wodiesan/senior_design_spring/documentation/latex_calculations/main.tex

\documentclass[12pt]{article}
%\usepackage{fontspec}
%\usepackage[utf8]{inputenc}

\usepackage[margin=1in]{geometry}

\usepackage{graphicx}
\usepackage{amsmath}
\usepackage{float}
\usepackage{xfrac}
%\usepackage{subfig}
\usepackage{subcaption}
\captionsetup{belowskip=12pt,aboveskip=4pt}
\usepackage{booktabs}
\usepackage{enumitem}
\usepackage{csquotes}

\usepackage{amsmath}
\usepackage{mathptmx}
\usepackage{helvet}
\renewcommand{\familydefault}{\sfdefault}
\usepackage{verbatim}
\usepackage{gensymb}
\usepackage{setspace}
\usepackage{booktabs}
\usepackage{hyperref}

\usepackage{listings}
\usepackage{color}
\definecolor{rp}{rgb}{0.47, 0.32, 0.66}
\definecolor{rb}{rgb}{0.25, 0.41, 0.88}
\definecolor{tp}{rgb}{0.4, 0.01, 0.24}
\definecolor{lightgrey}{rgb}{0.9,0.9,0.9}
\definecolor{darkgreen}{rgb}{0,0.6,0}

\usepackage{fancyhdr}
\pagestyle{fancy}
\cfoot{Confidential $\mid$ ELEC4500-2016-Calc Rev. 2}
\rfoot{\thepage}

\usepackage{multicol} % Required for splitting text into multiple columns
\setlength{\columnsep}{1cm}
\usepackage[toc]{glossaries}
\usepackage[protrusion=true,expansion=true]{microtype} % Improves spacing
%\usepackage[bf,sf,center]{titlesec} % Required for modifying section titles - bold, sans-serif, centered
%\usepackage{fancyhdr} % Required for modifying headers and footers
%\usepackage{subfiles}

\usepackage[toc,page]{appendix}

%\makeglossaries
%\input{./glossary.tex}

\begin{document}\thispagestyle{empty}
\pagenumbering{gobble}
\input{./title.tex}
\titleTMB
\newpage
\doublespacing

%\documentclass[12pt]{article}
%\usepackage{graphicx}
%\usepackage{float}
%\usepackage{chngpage}
%\addtolength{\topmargin}{-.5in}
%\textheight = 650pt
%\usepackage{helvet}
%\renewcommand{\familydefault}{\sfdefault}

%\begin{document}

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

%\newpage

%----------------------------------------------------------------------
% Abstract and Table of Contents
%----------------------------------------------------------------------
\begin{abstract}\thispagestyle{empty}

Technical specifications, i.e. calculations, breadboard diagrams, schematics, PCB layout design, and program flowcharts for a Raspberry Pi 2-based home surveillance system is outlined in this document. This system is designed to allow a homeowner to record digital video--through low-ambient lighting environments--when an adjustable motion threshold is surpassed. The system will include human and vehicle detection features. Recorded videos will be cataloged by the object type that activated the camera, i.e. human, vehicle, and others. This proposed functionality will allow a homeowner to quickly access their database of video data through categorical ``bookmarks'' based on metadata such as date, time, and type of object. The result is a lightweight, customizable, and scalable home surveillance system that remains inexpensive for storage. 

\end{abstract}

\newpage

\tableofcontents

%\newpage

\listoffigures

\listoftables

\newpage

%---------------------------------------------------------------------
% Intro
%---------------------------------------------------------------------
\pagenumbering{arabic}
%\section{Problem Statement and Motivation}

%\newpage
%\section{Appendix}
%\pagenumbering{roman}

%\newpage
\addcontentsline{toc}{section}{\nameref{sec:calc}}
\input{calculations}

%\newpage
%\addcontentsline{toc}{section}{\nameref{sec:haar}}
%\input{haar}

\newpage
\addcontentsline{toc}{section}{\nameref{sec:bbIter}}
\input{bbIterations}

\newpage
\addcontentsline{toc}{section}{\nameref{sec:schem}}
\input{schematics}

\newpage
\addcontentsline{toc}{section}{\nameref{sec:flow}}
\input{flowcharts}

\newpage
\addcontentsline{toc}{section}{\nameref{sec:manufDev}}
\input{manufDev}

%\newpage
%\addcontentsline{toc}{section}{\nameref{sec:db}}
%\input{database}

\newpage
%\begin{multicols}{2}
%\begin{onehalfspacing}
%\printglossary
%\end{onehalfspacing}
%\end{multicols}

%\newpage

%\input{glossary}

\addcontentsline{toc}{section}{References}
\input{bibl}

\end{document}
