wodiesan/senior_design_spring/documentation/latex_prototype/pics/Case_RPi_Exploded.PNG

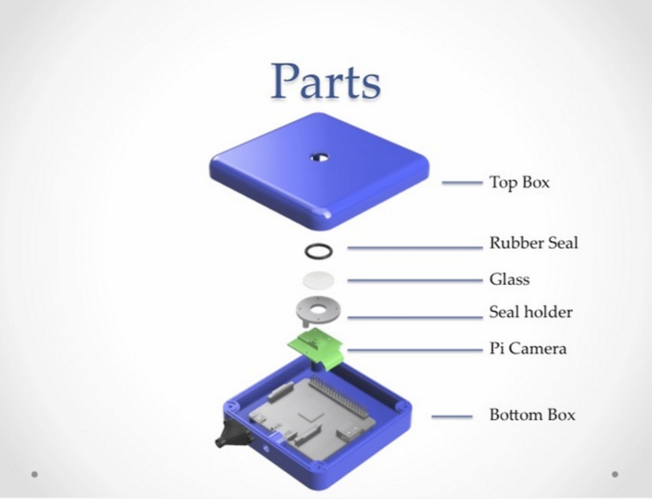
documentation/latex_prototype/pics/Case_RPi_Exploded.PNG
