wodiesan/senior_design_spring/documentation/latex_prototype/pics/eval_in_12ft_nelson.jpg

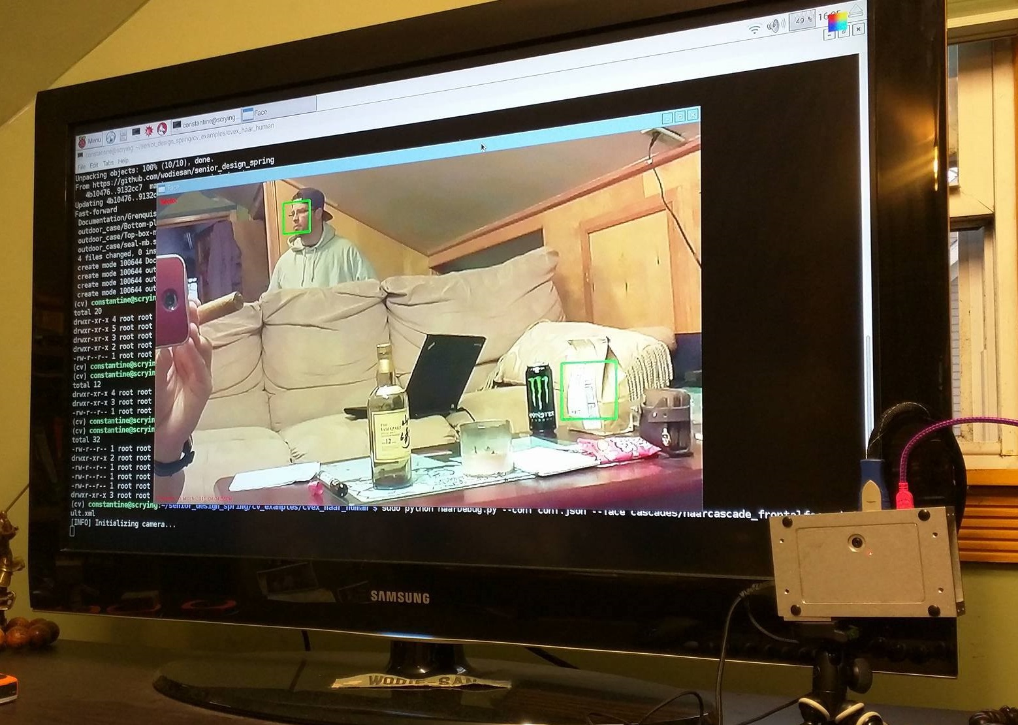
documentation/latex_prototype/pics/eval_in_12ft_nelson.jpg
