wodiesan/senior_design_spring/documentation/latex_prototype/pics/eval_in_invariant_nose.jpg

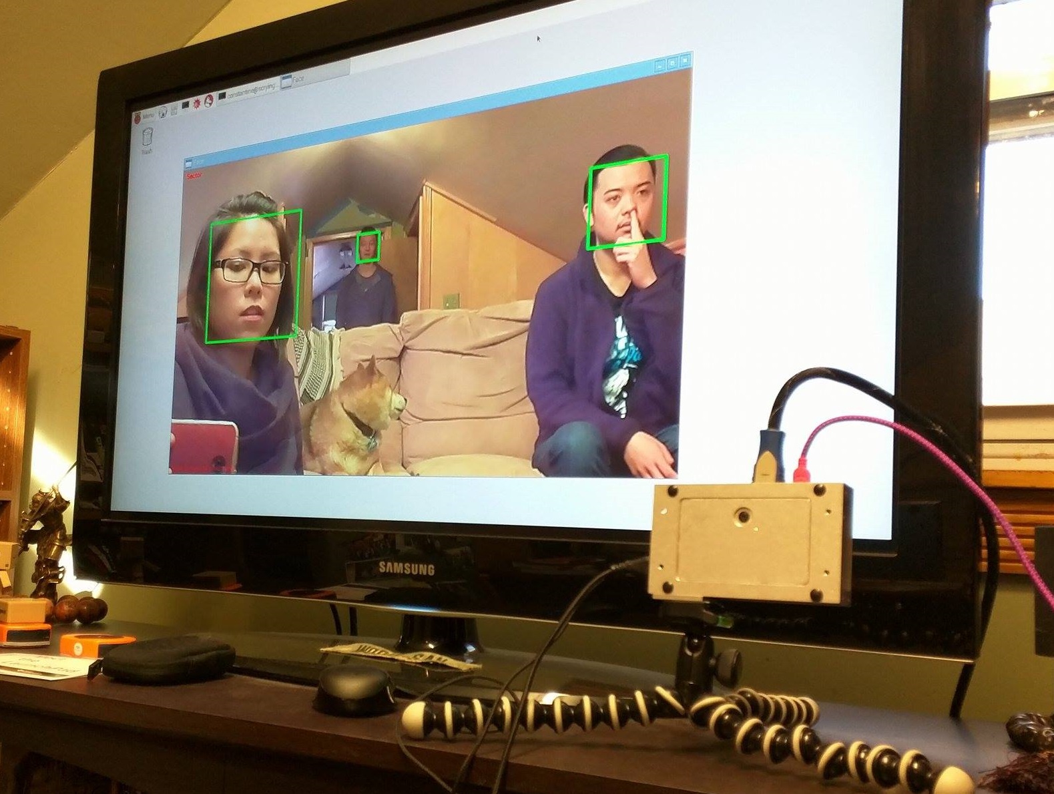
documentation/latex_prototype/pics/eval_in_invariant_nose.jpg
