wodiesan/senior_design_spring/documentation/latex_prototype/pics/eval_out_nightIR_face1.jpg

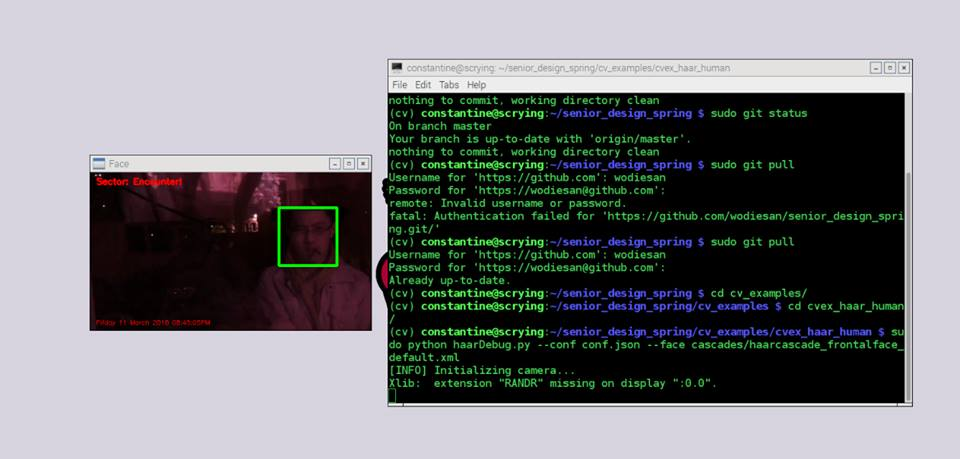
documentation/latex_prototype/pics/eval_out_nightIR_face1.jpg
