wodiesan/senior_design_spring/cv_methods_isolated/cv_hog_svm_ped/ped.py

#!/usr/bin/env python
# sys added to access default site packages folder.
import sys
sys.path.append('/usr/local/lib/python2.7/site-packages')

"""
ELEC4500 Senior Design 1 | Spring 2016
Stand-alone human silhouette detection through HOG + Linear SVM.
Utilizes the Raspberry Pi 2 camera module for detection.
"""

#from __future__ import print_function
from imutils.object_detection import non_max_suppression
from imutils import paths
from picamera.array import PiRGBArray
from picamera import PiCamera
import numpy as np
import argparse
import imutils
import cv2
import datetime
import json
import time
import warnings

# Front matter.
__author__ = "Sze 'Ron' Chau"
__copyright__ = "Copyright 2016, Sze 'Ron' Chau"
__credits__ = "Adrian Rosebrock, Ph.D."
__license__ = "MIT"
__version__ = "0.0.1"
__maintainer__ = "Sze 'Ron' Chau"
__email__ = "wodiesan@gmail.com"
__status__ = "Prototype"

# Construct the argument parse.
ap = argparse.ArgumentParser()
ap.add_argument("-c", "--conf", required=True, help="JSON camera config.")
args = vars(ap.parse_args())

# Supress expected warning and access camera config file.
warnings.filterwarnings("ignore")
conf = json.load(open(args["conf"]))

# Populate JSON camera config.
camera = PiCamera()
camera.resolution = tuple(conf["resolution"])
camera.framerate = conf["fps"]
camera.rotation = conf["rotation"]
print 'Initializing camera module.'

# Complete init for camera.
rawCapture = PiRGBArray(camera, size=tuple(conf["resolution"]))
time.sleep(conf["camera_warmup_time"])

# Init HOG detector, set SVM to pre-trained human silhouette detector.
hog = cv2.HOGDescriptor()
hog.setSVMDetector(cv2.HOGDescriptor_getDefaultPeopleDetector())

# Capture frames from camera module.
for f in camera.capture_continuous(rawCapture, format="bgr",
                                   use_video_port=True):

    # Grab raw numpy array representing the img.
    # Init timestamp and on-screen status text.
    frame = f.array
    # frameClone = frame.copy()
    timestamp = datetime.datetime.now()
    text = "Clear"

    # Resize frame, preprocess to grayscale and Gaussian blur.
    frame = imutils.resize(frame, width=conf["frame_width"])
    # gray = cv2.cvtColor(frame, cv2.COLOR_BGR2GRAY)
    gray = cv2.GaussianBlur(frame, (21, 21), 0)

# STATIC IMAGES: Loop over the image paths.
# for imagePath in paths.list_images(args["images"]):
    # Load the image and resize it to:
    # 1. Reduce detection time.
    # 2. Improve detection accuracy.
    # image = cv2.imread(imagePath)
    # image = imutils.resize(image, width=min(400, image.shape[1]))
    # orig = image.copy()

    # Save a clone of the frame before preprocessing. Used for live preview.
    frameClone = frame.copy()

    # Detect silhouettes in frame. Adjust scale based on camera location.
    # winStride is the sliding window step size coordinates.
    # A > scale val evals < layers, t.f. it runs faster but less accurate.
    # weights is the confidence val returned from SVG per detection.
    (bodyRects, weights) = hog.detectMultiScale(gray, winStride=(4, 4),
                                                padding=(8, 8), scale=1.05)

    # Draw bounding boxes on detected regions of the clone frame.
    for (x, y, w, h) in bodyRects:
        cv2.rectangle(frameClone, (x, y), (x + w, y + h), (0, 0, 255), 2)

    # Apply non-maxima suppression to bounding boxes using a large overlap
    # thresh to try to maintain overlapping boxes.
    bodyRects = np.array([[x, y, x + w, y + h] for (x, y, w, h) in bodyRects])
    pick = non_max_suppression(bodyRects, probs=None, overlapThresh=0.65)

    # Draw the final bounding boxes on the clone.
    for (xA, yA, xB, yB) in pick:
        cv2.rectangle(frameClone, (xA, yA), (xB, yB), (0, 255, 0), 2)
        text = 'Silhouette'

    # Display data RE: # of bounding boxes.
    print("{} original boxes, {} after suppression".format(
          len(bodyRects), len(pick)))
    ts = timestamp.strftime("%A %d %B %Y %I:%M:%S%p")
    cv2.putText(frameClone, "Sector: {}".format(text), (10, 20),
                cv2.FONT_HERSHEY_SIMPLEX, 0.5, (0, 0, 255), 2)
    cv2.putText(frameClone, ts, (10, frame.shape[0] - 10),
                cv2.FONT_HERSHEY_SIMPLEX, 0.35, (0, 0, 255), 1)

    # Display live preview for the frames.
    # Verify whether the frames should be displayed to screen.
    if conf["show_video"]:
        cv2.imshow("Silhouette", frameClone)
        key = cv2.waitKey(1) & 0xFF

        # Pressing 'q' at anytime to terminate and exit.
        if key == ord("q"):
            break

    # Clear stream in preparation for the next frame.
    rawCapture.truncate(0)

    # cv2.imshow("Before NMS", orig)
    # cv2.imshow("After NMS", image)
    # cv2.waitKey(0)

# Previous work. Ignore.
# # import the necessary packages
# # sys added to access default site packages folder.
# import sys
# sys.path.append('/usr/local/lib/python2.7/site-packages')

# from picamera.array import PiRGBArray
# from picamera import PiCamera
# import time
# import cv2

# # initialize the camera and grab a reference to the raw camera capture
# camera = PiCamera()
# camera.resolution = (640, 480)
# camera.framerate = 32
# rawCapture = PiRGBArray(camera, size=(640, 480))

# # allow the camera to warmup
# time.sleep(0.1)

# # capture frames from the camera
# for frame in camera.capture_continuous(rawCapture, format="bgr", use_video_port=True):
#   # grab the raw NumPy array representing the image, then initialize the timestamp
#   # and occupied/unoccupied text
#   image = frame.array

#   # show the frame
#   cv2.imshow("Frame", image)
#   key = cv2.waitKey(1) & 0xFF

#   # clear the stream in preparation for the next frame
#   rawCapture.truncate(0)

#   # if the `q` key was pressed, break from the loop
#   if key == ord("q"):
#       break
